dnewcome/megamop/cad/build/concept_sketch_c.png

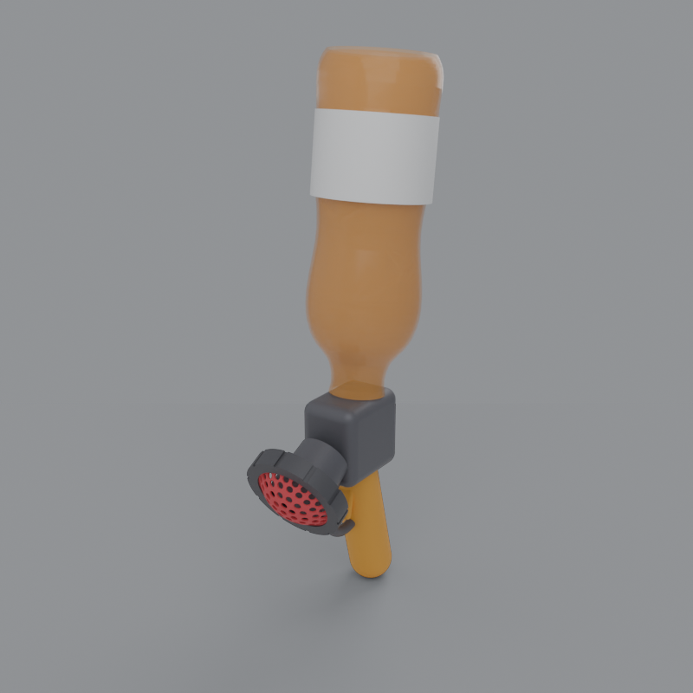
cad/build/concept_sketch_c.png
