dnewcome/megamop/cad/build/glb_preview.png

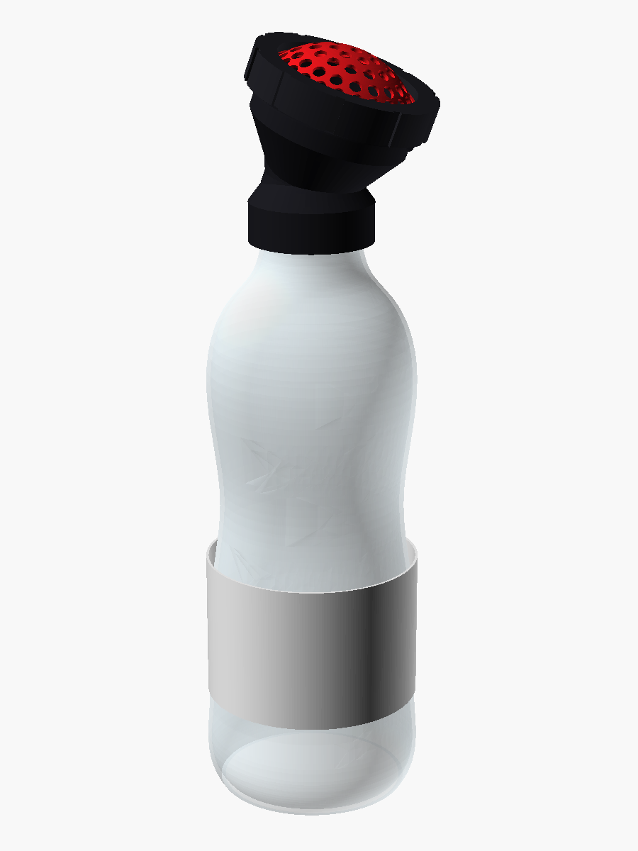
cad/build/glb_preview.png
