dnewcome/megamop/cad/build/megamop_section.png

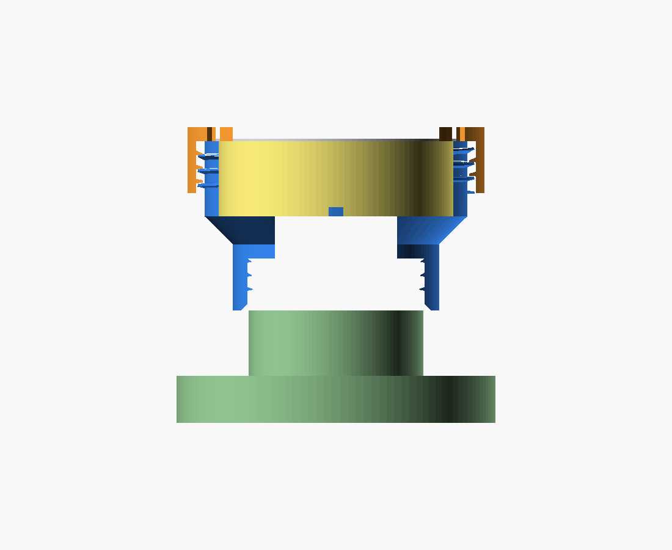
cad/build/megamop_section.png
