dnewcome/megamop/cad/build/thread_mesh.png

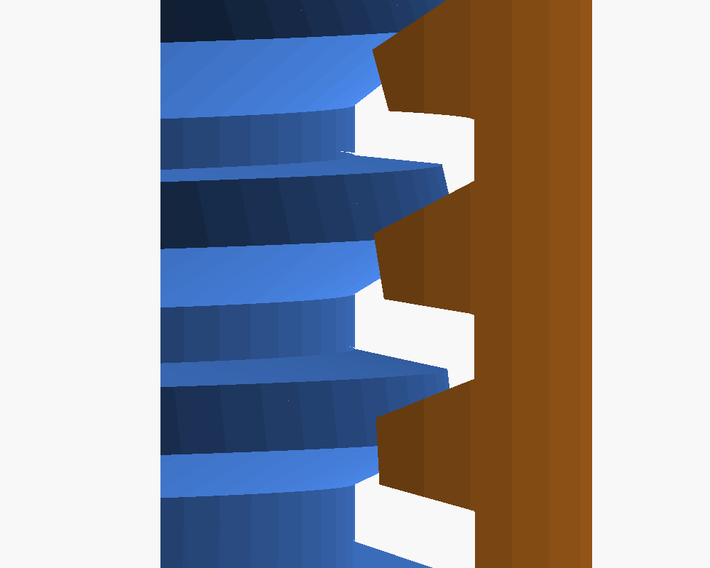
cad/build/thread_mesh.png
